FECstudios/deskbuddy/schematics/deskbuddy.kicad_sch

## KiCad design schematics/deskbuddy.kicad_sch (2026-06-23)

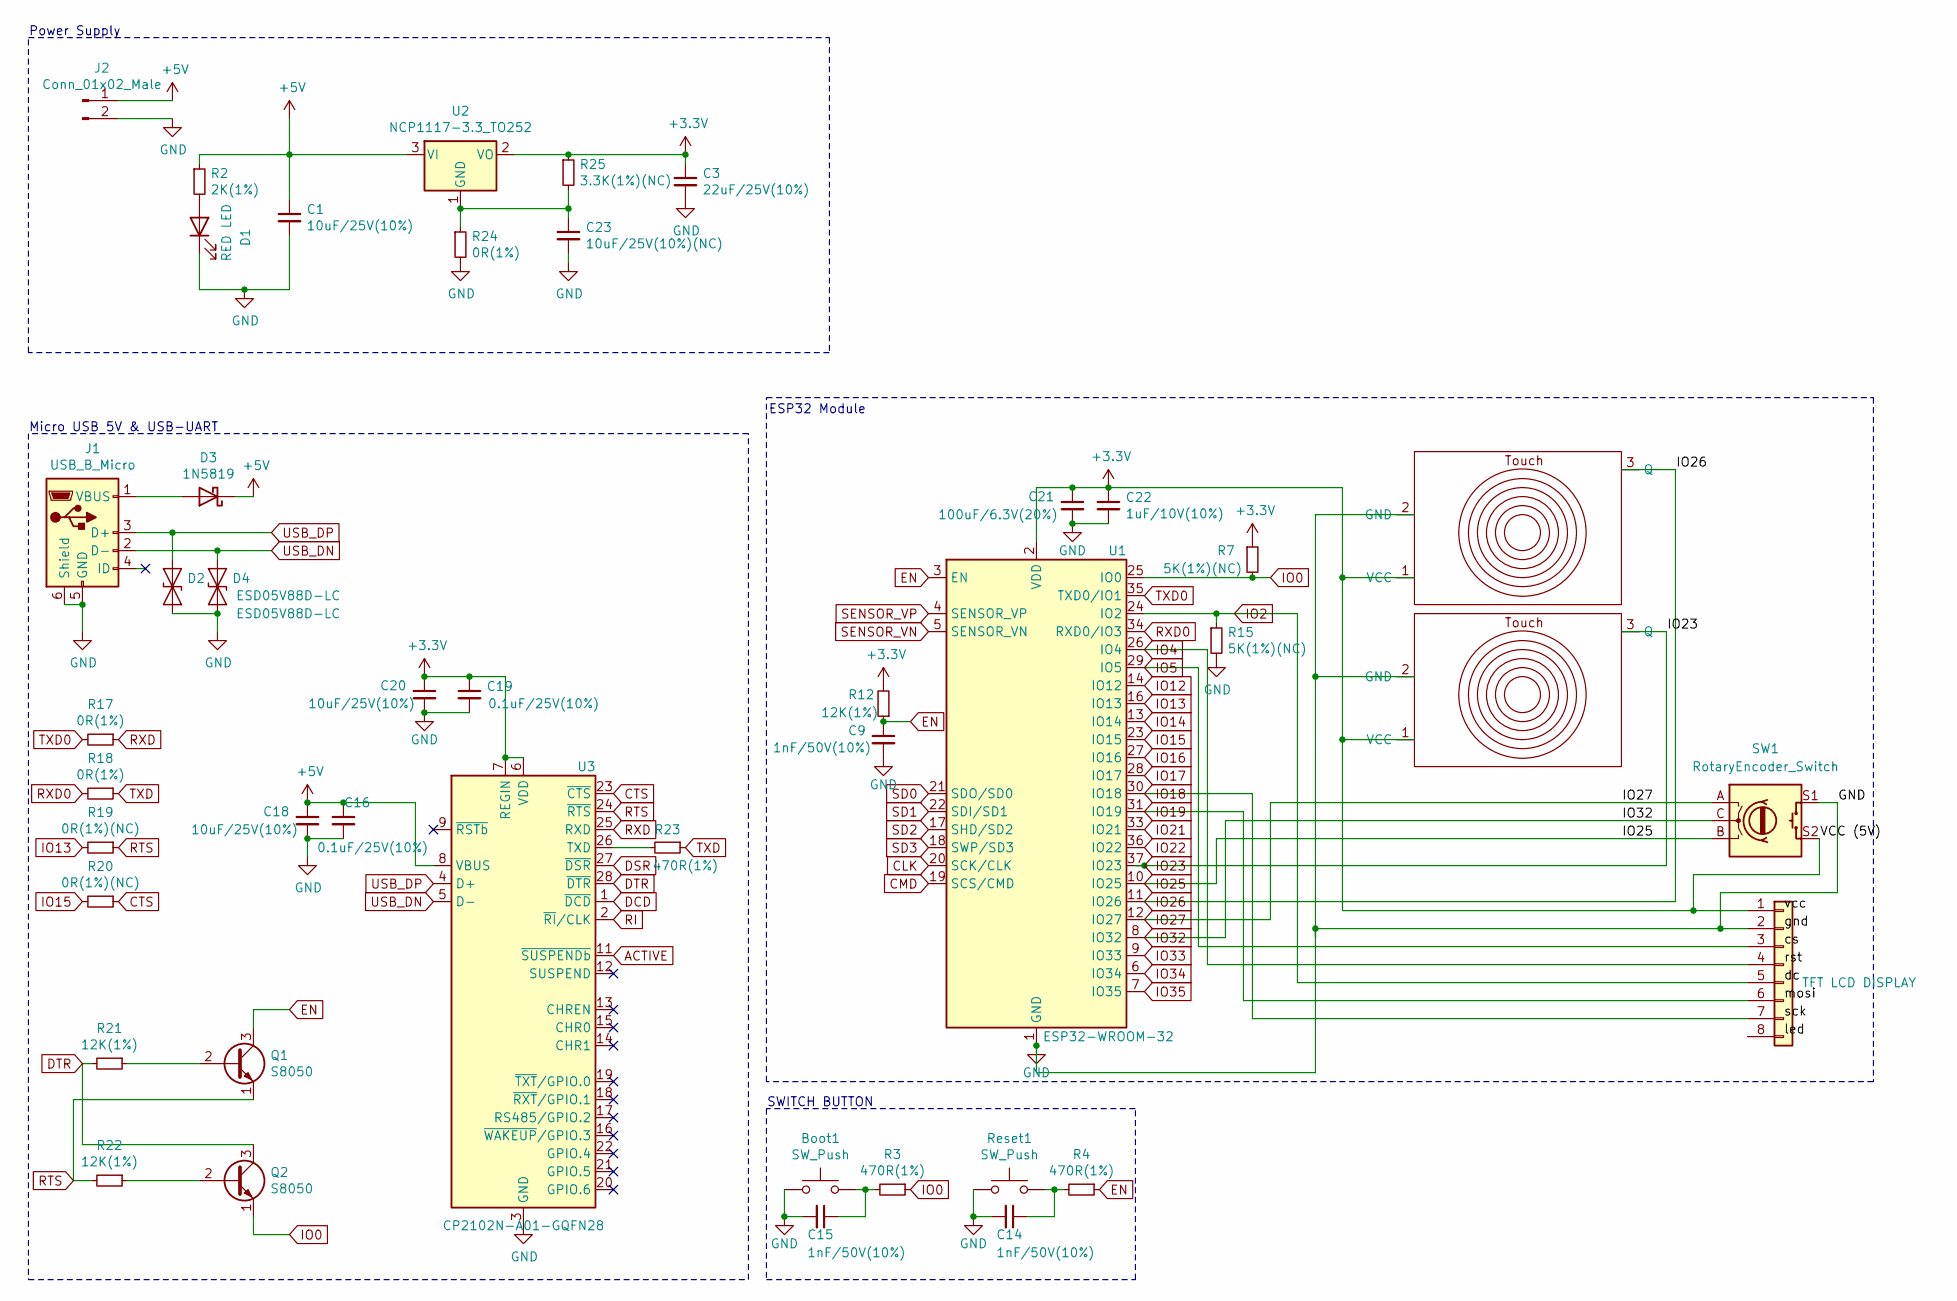
[picture p7: schematic deskbuddy.kicad_sch]

Parts:
Boot1: SW_Push; SW_Push_SPST_NO_Alps_SKRK
C1, C18, C20: 10uF/25V(10%); C_0603_1608Metric
C3: 22uF/25V(10%); C_0603_1608Metric
C9, C14, C15: 1nF/50V(10%); C_0402_1005Metric
C16, C19: 0.1uF/25V(10%); C_0402_1005Metric
C21: 100uF/6.3V(20%); C_0603_1608Metric
C22: 1uF/10V(10%); C_0402_1005Metric
C23: 10uF/25V(10%)(NC); C_0402_1005Metric
D1: RED LED; LED_0603_1608Metric
D2, D4: ESD05V88D-LC; D_0402_1005Metric
D3: 1N5819; D_0402_1005Metric
J1: USB_B_Micro; USB_Micro-B_Molex_47346-0001
J2: Conn_01x02_Male; JST_EH_B2B-EH-A_1x02_P2.50mm_Vertical
J3: TFT LCD DISPLAY
Q1, Q2: S8050; SOT-23
R2: 2K(1%); R_0402_1005Metric
R3, R4: 470R(1%); R_0402_1005Metric
R7, R15: 5K(1%)(NC); R_0402_1005Metric
R12, R21, R22: 12K(1%); R_0402_1005Metric
R17, R18, R24: 0R(1%); R_0402_1005Metric
R19, R20: 0R(1%)(NC); R_0402_1005Metric
R23: 470R(1%); C_0402_1005Metric
R25: 3.3K(1%)(NC); R_0402_1005Metric
Reset1: SW_Push; SW_Push_SPST_NO_Alps_SKRK
SW1: RotaryEncoder_Switch
U1: ESP32-WROOM-32
U2: NCP1117-3.3_TO252; SOT-223
U3: CP2102N-A01-GQFN28; QFN-28-1EP_5x5mm_P0.5mm_EP3.35x3.35mm
U4, U5: (no value)

Connections:
+3.3V: C3.1, C19.1, C20.1, C21.1, C22.1, J3.1, R7.1, R12.2, R25.1, SW1.S2, U1.2 (VDD), U2.2 (VO), U3.6 (VDD), U3.7 (REGIN), U4.1 (VCC), U5.1 (VCC)
+5V: C1.1, C16.1, C18.1, D3.1 (K), J2.1, R2.1, U2.3 (VI), U3.8 (VBUS)
ACTIVE: U3.11 (~SUSPENDb)
CLK: U1.20 (SCK/CLK)
CMD: U1.19 (SCS/CMD)
CTS: R20.1, U3.23 (~CTS)
DCD: U3.1 (~DCD)
DSR: U3.27 (~DSR)
DTR: Q2.3 (C), R21.2, U3.28 (~DTR)
EN: C9.1, Q1.3 (C), R4.1, R12.1, U1.3 (EN)
GND: Boot1.1, C1.2, C3.2, C9.2, C14.2, C15.2, C16.2, C18.2, C19.2, C20.2, C21.2, C22.2, C23.2, D1.1 (K), D2.2 (A2), D4.2 (A2), J1.5 (GND), J1.6 (Shield), J2.2, J3.2, R15.2, R24.2, Reset1.1, SW1.S1, U1.1 (GND), U1.15 (GND), U1.38 (GND), U1.39 (GND), U3.3 (GND), U3.29 (GND), U4.2 (GND), U5.2 (GND)
IO0: Q2.1 (E), R3.1, R7.2, U1.25 (IO0)
IO2: J3.5, R15.1, U1.24 (IO2)
IO4: J3.4, U1.26 (IO4)
IO5: J3.3, U1.29 (IO5)
IO12: U1.14 (IO12)
IO13: R19.2, U1.16 (IO13)
IO14: U1.13 (IO14)
IO15: R20.2, U1.23 (IO15)
IO16: U1.27 (IO16)
IO17: U1.28 (IO17)
IO18: J3.7, U1.30 (IO18)
IO19: J3.6, U1.31 (IO19)
IO21: U1.33 (IO21)
IO22: U1.36 (IO22)
IO23: U1.37 (IO23), U5.3 (Q)
IO25: SW1.B, U1.10 (IO25)
IO26: U1.11 (IO26), U4.3 (Q)
IO27: SW1.A, U1.12 (IO27)
IO32: SW1.C, U1.8 (IO32)
IO33: U1.9 (IO33)
IO34: U1.6 (IO34)
IO35: U1.7 (IO35)
unnamed: Boot1.2, C15.1, R3.2
unnamed: C14.1, R4.2, Reset1.2
unnamed: C23.1, R24.1, R25.2, U2.1 (GND)
unnamed: D1.2 (A), R2.2
unnamed: D3.2 (A), J1.1 (VBUS)
unnamed: Q1.2 (B), R21.1
unnamed: Q2.2 (B), R22.1
unnamed: R23.2, U3.26 (TXD)
RI: U3.2 (~RI/CLK)
RTS: Q1.1 (E), R19.1, R22.2, U3.24 (~RTS)
RXD: R17.1, U3.25 (RXD)
RXD0: R18.2, U1.34 (RXD0/IO3)
SD0: U1.21 (SDO/SD0)
SD1: U1.22 (SDI/SD1)
SD2: U1.17 (SHD/SD2)
SD3: U1.18 (SWP/SD3)
SENSOR_VN: U1.5 (SENSOR_VN)
SENSOR_VP: U1.4 (SENSOR_VP)
TXD: R18.1, R23.1
TXD0: R17.2, U1.35 (TXD0/IO1)
USB_DN: D4.1 (A1), J1.2 (D-), U3.5 (D-)
USB_DP: D2.1 (A1), J1.3 (D+), U3.4 (D+)

Notes on the sheet:
Power Supply
SWITCH BUTTON
ESP32 Module
Micro USB 5V & USB-UART
